GenericLab/BioAmp-EXG-MedTechDIY/hardware/MASK/SolderPaste_line.png

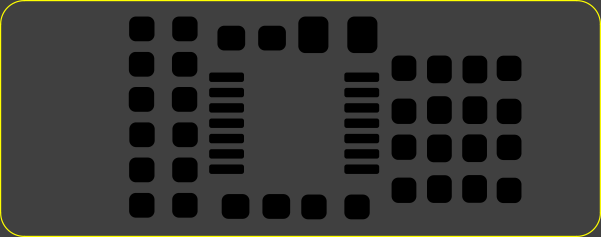
hardware/MASK/SolderPaste_line.png
